faunel/fan_controller/eeprom/src/default_settings.rs

pub(crate) const DEFAULT_SETTINGS_FAN: [[u16; 2]; 4] = [[35, 20], [45, 40], [55, 65], [70, 100]];
pub(crate) const DEFAULT_SETTINGS_BL: u16 = 6;
pub(crate) const DEFAULT_SETTINGS_NTC_NO: [u16; 4] = [1, 2, 3, 4];
